avetol/Proyecto_titulo/fotos ADC voltaje arduino nano/IMG_20211109_131354_1.jpg

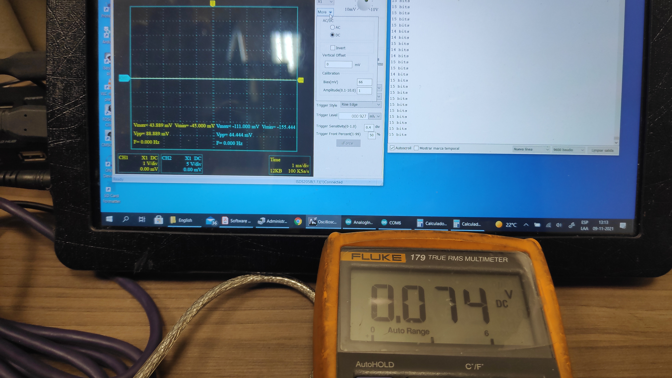
fotos ADC voltaje arduino nano/IMG_20211109_131354_1.jpg
