avetol/Proyecto_titulo/fotos ADC voltaje arduino nano/IMG_20211109_132629.jpg

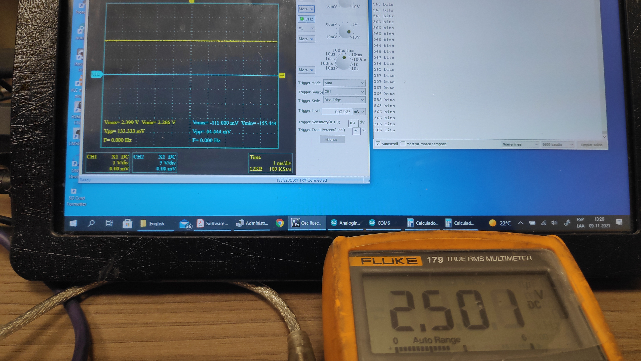
fotos ADC voltaje arduino nano/IMG_20211109_132629.jpg
