avetol/Proyecto_titulo/fotos ADC voltaje arduino nano/IMG_20211109_132730.jpg

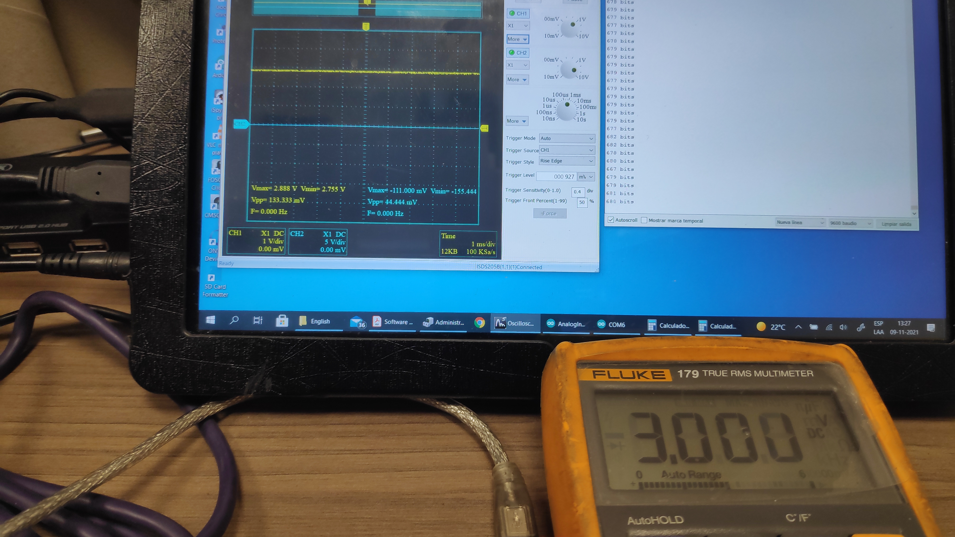
fotos ADC voltaje arduino nano/IMG_20211109_132730.jpg
