avetol/Proyecto_titulo/fotos ADC voltaje arduino nano/IMG_20211109_132839.jpg

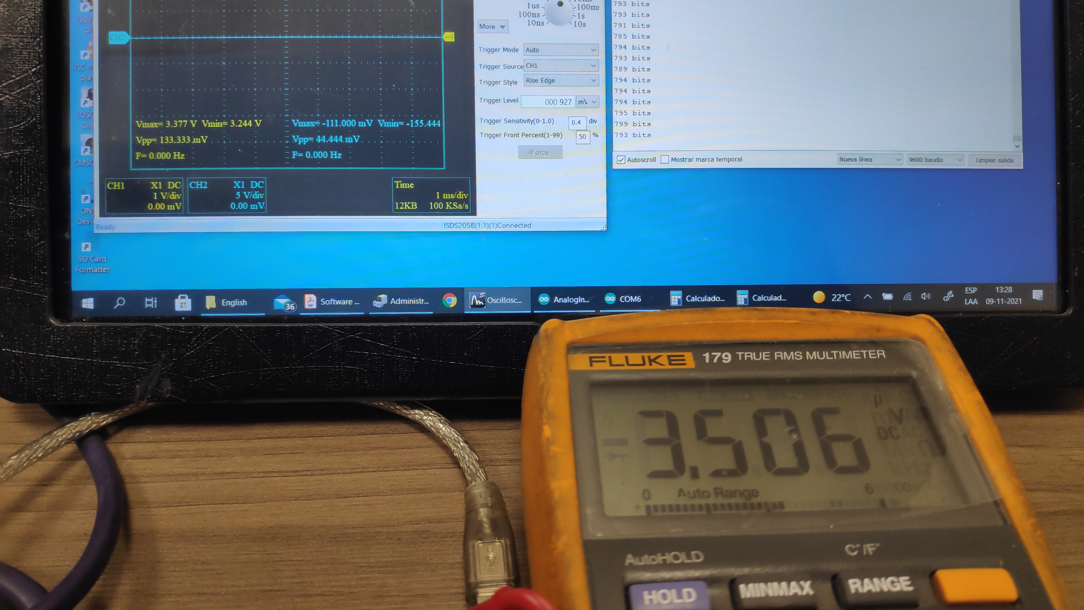
fotos ADC voltaje arduino nano/IMG_20211109_132839.jpg
