avetol/Proyecto_titulo/fotos ADC voltaje arduino nano/IMG_20211109_133153_1.jpg

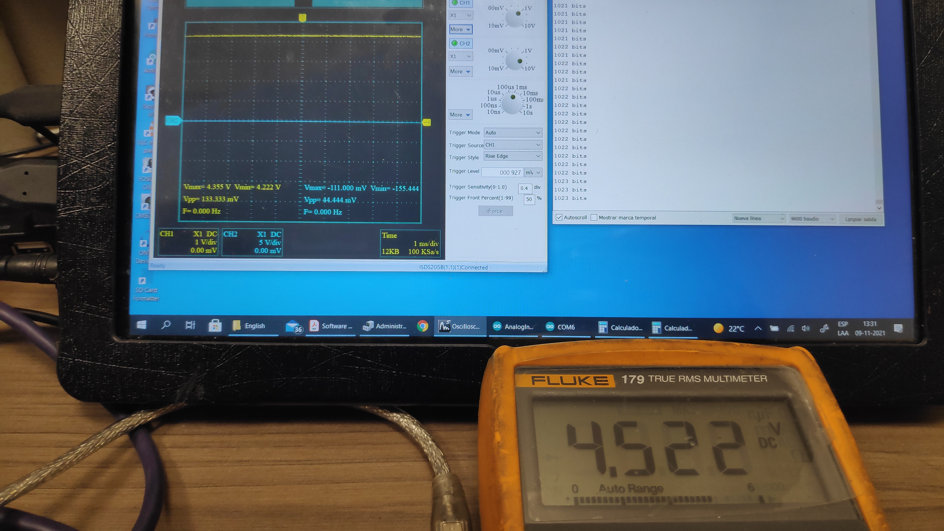
fotos ADC voltaje arduino nano/IMG_20211109_133153_1.jpg
