avetol/Proyecto_titulo/fotos ADC voltaje arduino nano/IMG_20211109_133818.jpg

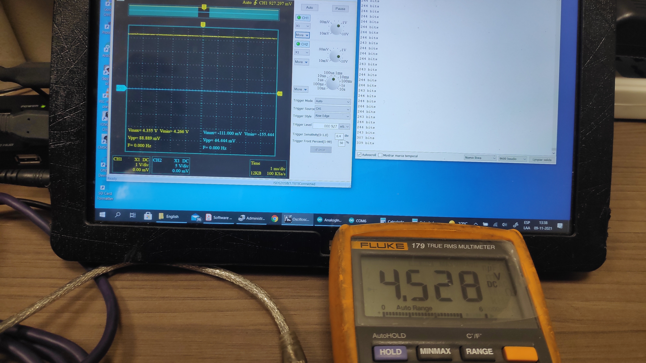
fotos ADC voltaje arduino nano/IMG_20211109_133818.jpg
