avetol/Proyecto_titulo/img/ilustracion 5 primer Indoor Diy.png

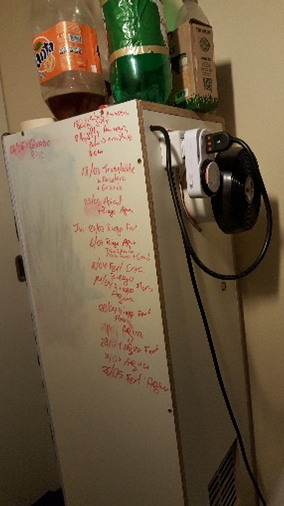
img/ilustracion 5 primer Indoor Diy.png
