avetol/Proyecto_titulo/img/ilustracion 6 interior primer Indoor con 2 sistemas de luces censored.png

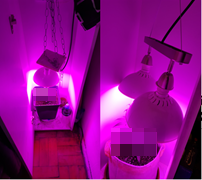
img/ilustracion 6 interior primer Indoor con 2 sistemas de luces censored.png
