avetol/Proyecto_titulo/img/ilustracion 10 cultivo en tierra con luz alta presion 1 censured.png

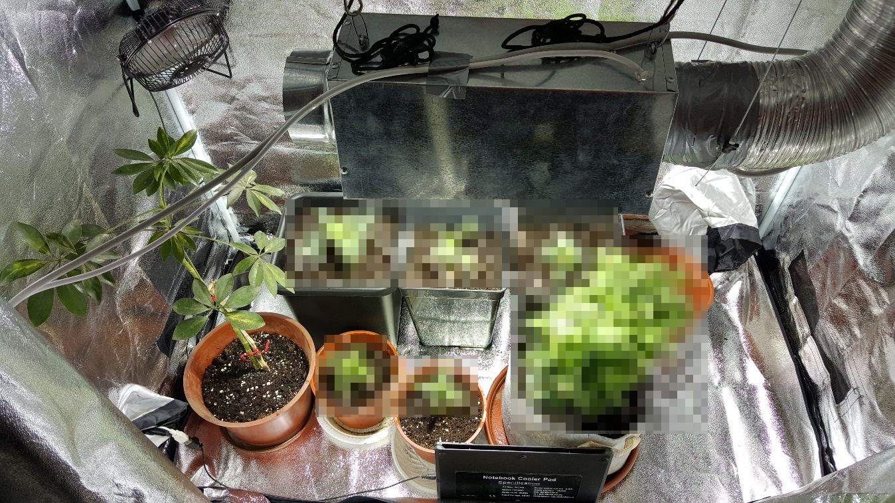
img/ilustracion 10 cultivo en tierra con luz alta presion 1 censured.png
