avetol/Proyecto_titulo/img/ilustracion 10 cultivo en tierra con luz alta presion 2 censored.png

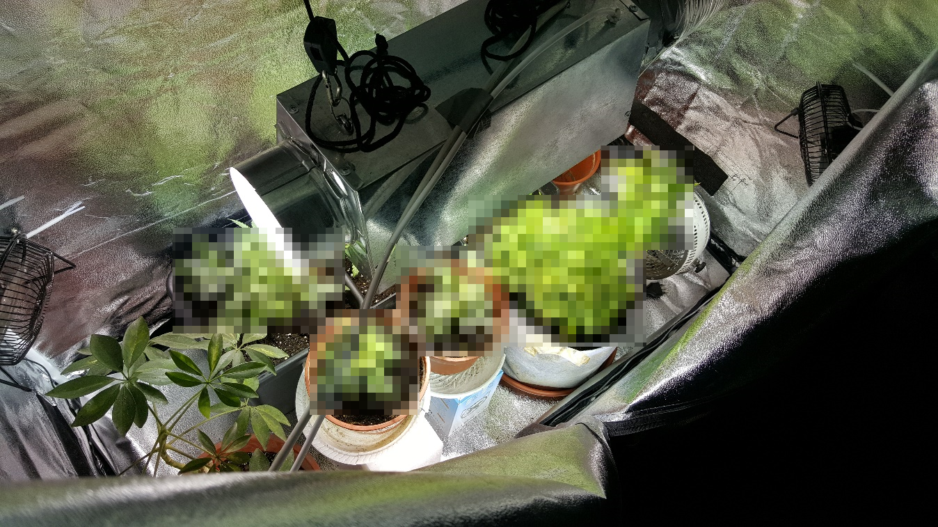
img/ilustracion 10 cultivo en tierra con luz alta presion 2 censored.png
