avetol/Proyecto_titulo/img/ilustracion 25 RTC DS1307.png

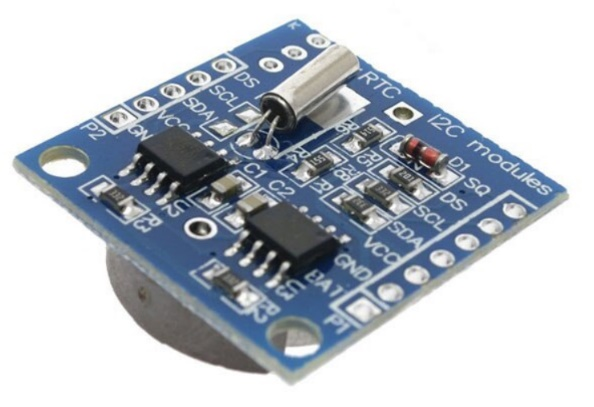
img/ilustracion 25 RTC DS1307.png
