avetol/Proyecto_titulo/img/ilustracion 26 Modulo Rele 5V4Output.png

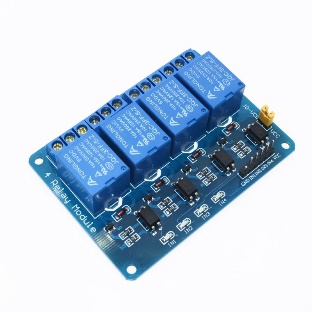
img/ilustracion 26 Modulo Rele 5V4Output.png
