avetol/Proyecto_titulo/img/ilustracion 36 Sensor T DS18b20.png

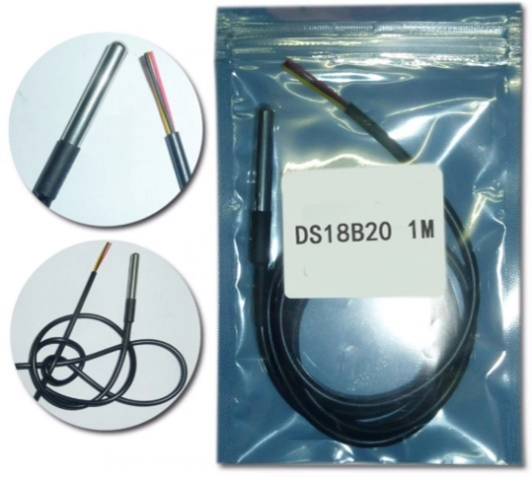
img/ilustracion 36 Sensor T DS18b20.png
