avetol/Proyecto_titulo/img/ilustracion 40 modulo control Sonda PH.png

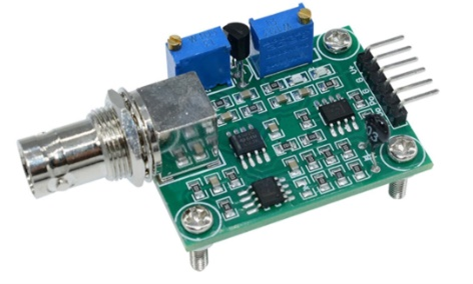
img/ilustracion 40 modulo control Sonda PH.png
