avetol/Proyecto_titulo/img/ilustracion 42 Pulverizador agua.png

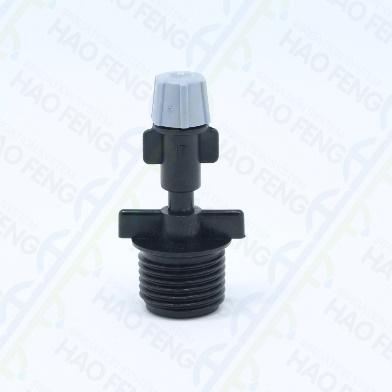
img/ilustracion 42 Pulverizador agua.png
