avetol/Proyecto_titulo/img/ilustracion 47 Modulo Ventilación y Monitoreo.png

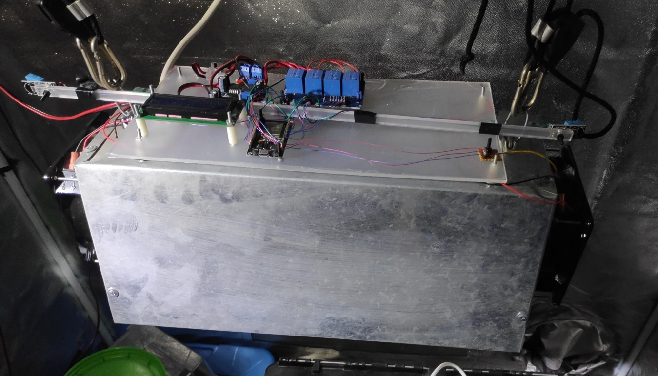
img/ilustracion 47 Modulo Ventilación y Monitoreo.png
