avetol/Proyecto_titulo/img/ilustracion 49 Sensor Iac ACS712.png

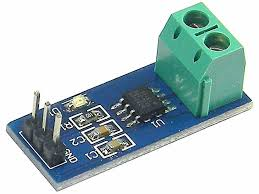
img/ilustracion 49 Sensor Iac ACS712.png
