avetol/Proyecto_titulo/img/ilustracion 50 Sofware programacion.png

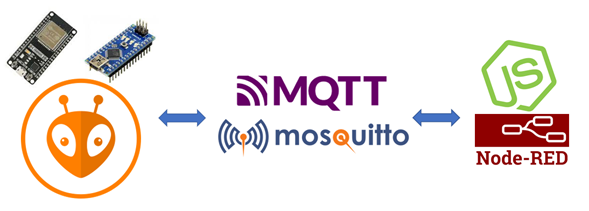
img/ilustracion 50 Sofware programacion.png
