avetol/Proyecto_titulo/img/ilustracion 52 AC sensor con punto medio 2.5V.PNG

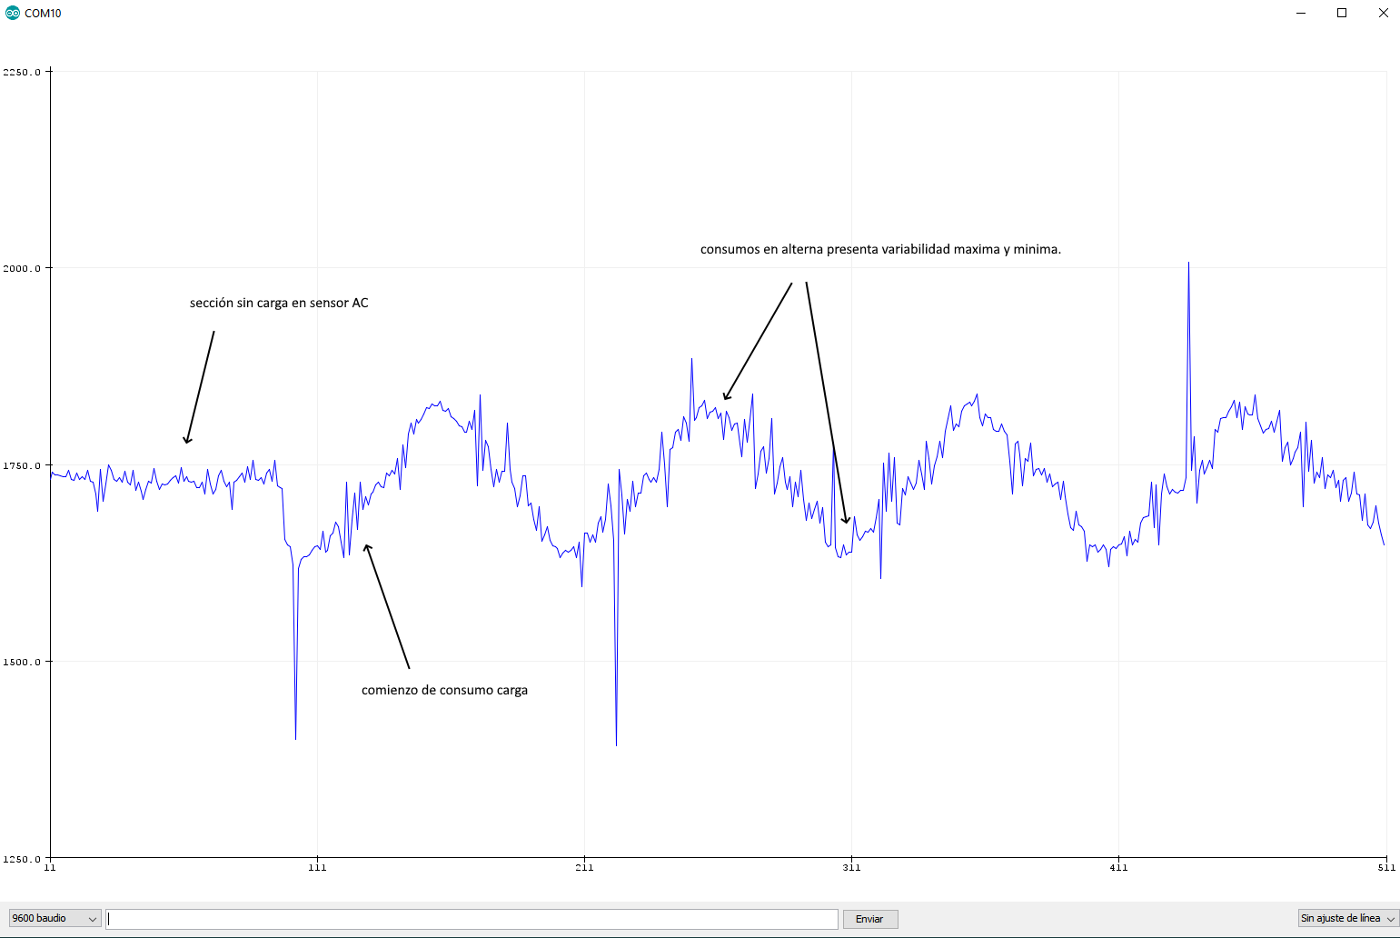
img/ilustracion 52 AC sensor con punto medio 2.5V.PNG
