avetol/Proyecto_titulo/img/ilustracion 52 punto medio con capacitor.PNG

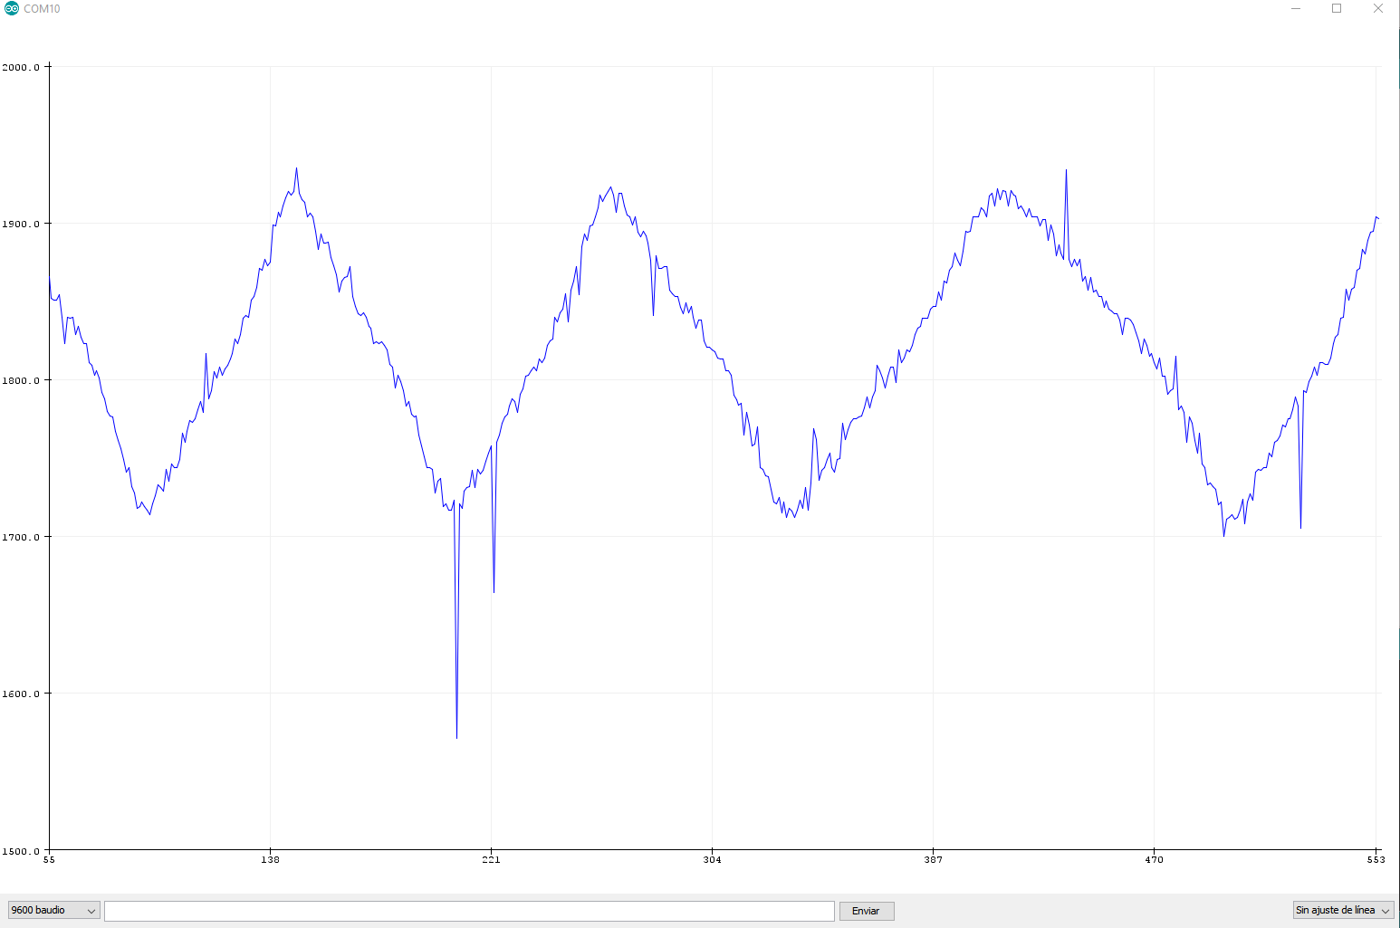
img/ilustracion 52 punto medio con capacitor.PNG
