avetol/Proyecto_titulo/img/ilustracion 54 BackEnd Node-Red.PNG

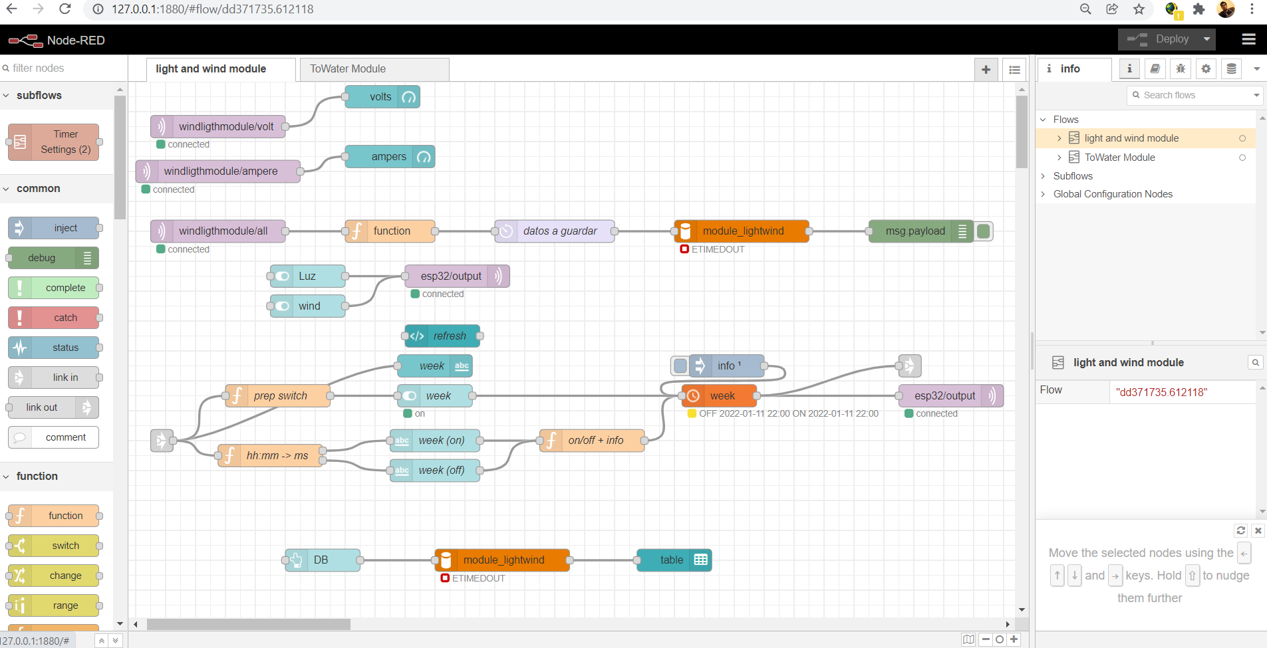
img/ilustracion 54 BackEnd Node-Red.PNG
