avetol/Proyecto_titulo/img/ilustracion 55 FrontEnd Node-Red.PNG

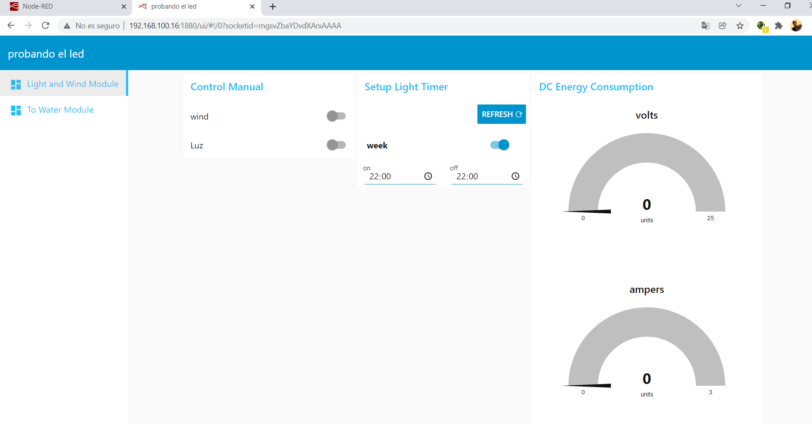
img/ilustracion 55 FrontEnd Node-Red.PNG
