avetol/Proyecto_titulo/img/ilustracion 57 ajustes nodo MQTT broker.png

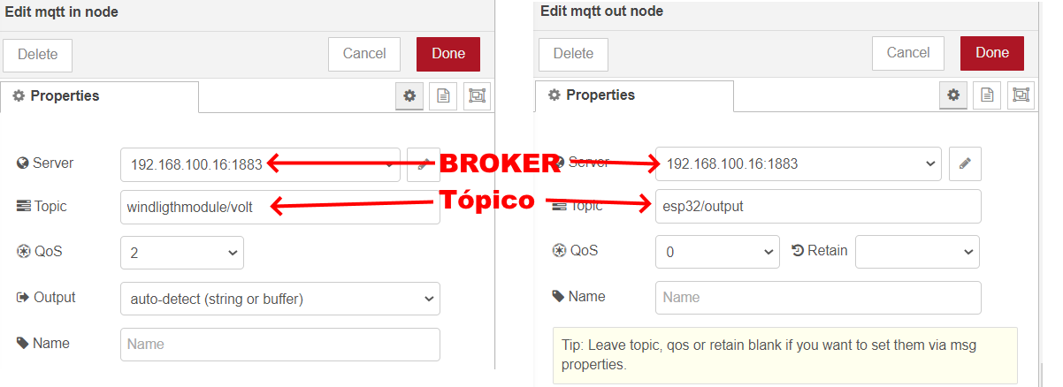
img/ilustracion 57 ajustes nodo MQTT broker.png
