avetol/Proyecto_titulo/img/ilustracion 59 Ajuste Broker MQTT arduino.png

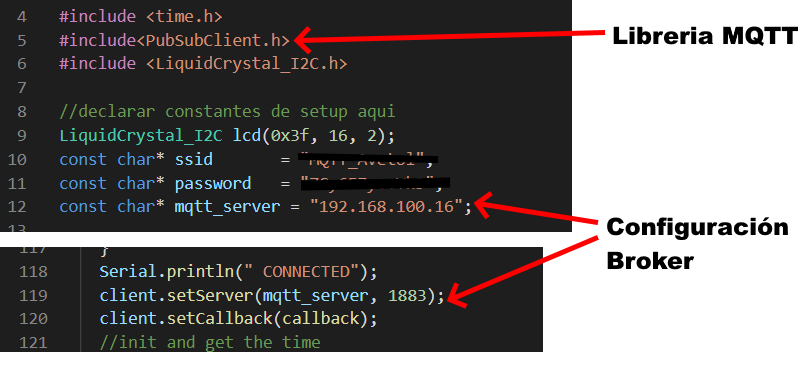
img/ilustracion 59 Ajuste Broker MQTT arduino.png
